OliverSwift/SwiftZigbeeSoilMoistureSensor/include/adc.h

#ifndef _ADC_H_
#define _ADC_H_

/*
 * Copyright (c) 2024 Olivier DEBON
 *
 * SPDX-License-Identifier: AGPL-3.0-or-later
 */

int adc_setup(void); // Set up ADC drivers and inputs
int32_t adc_probe(void); // Read Moisture Probe value, returns mv
uint8_t adc_battery(void); // Read Battery voltage, returns percentage

#endif
